AlbrechtL/10BASE-T1L/png/before pd xfmr w pd in reset 31V.png

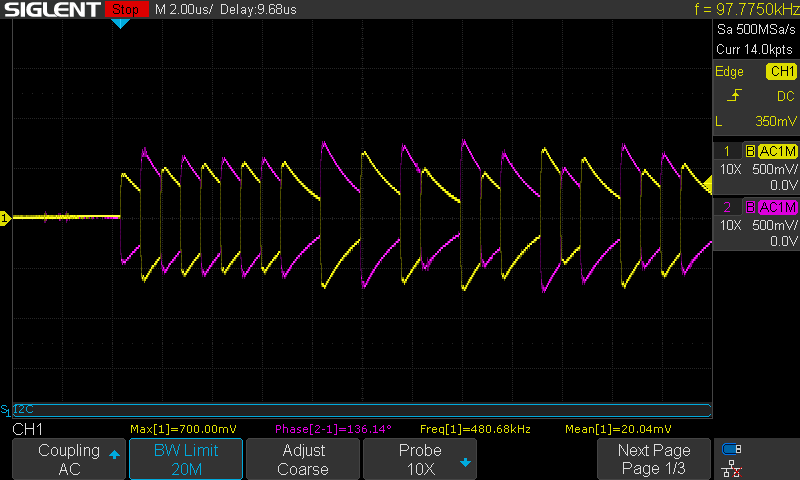
png/before pd xfmr w pd in reset 31V.png
