AlbrechtL/10BASE-T1L/png/SDS00017.png

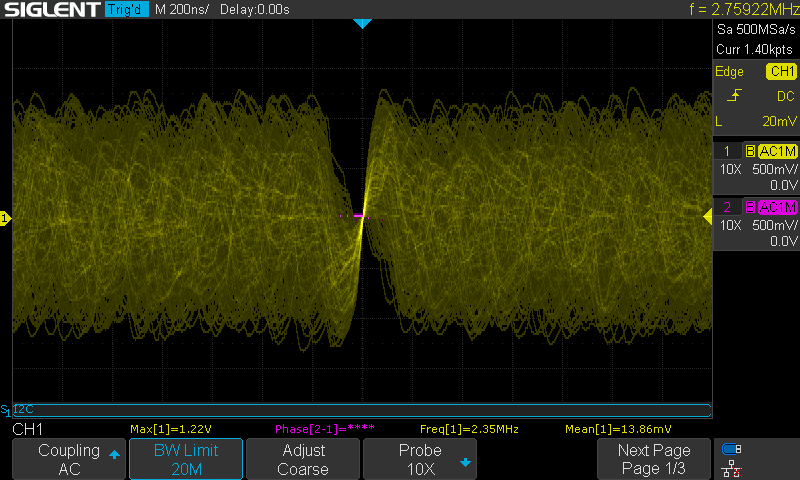
png/SDS00017.png
