AlbrechtL/10BASE-T1L/png/SDS00018.png

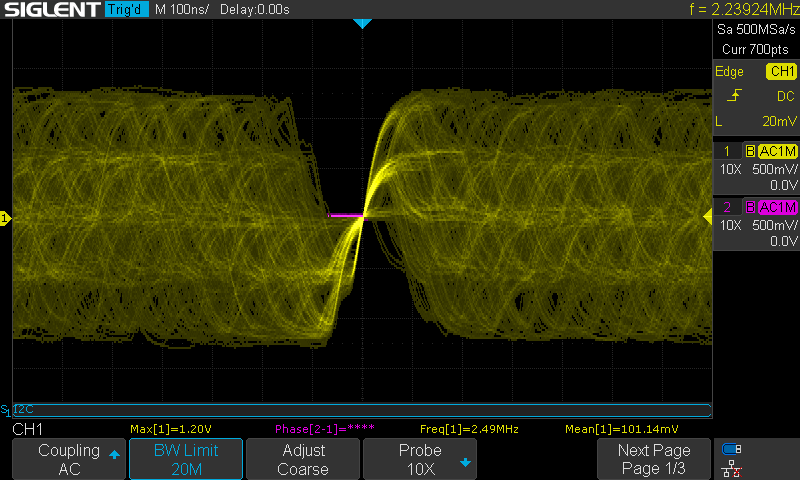
png/SDS00018.png
