AlbrechtL/10BASE-T1L/png/SDS00020.png

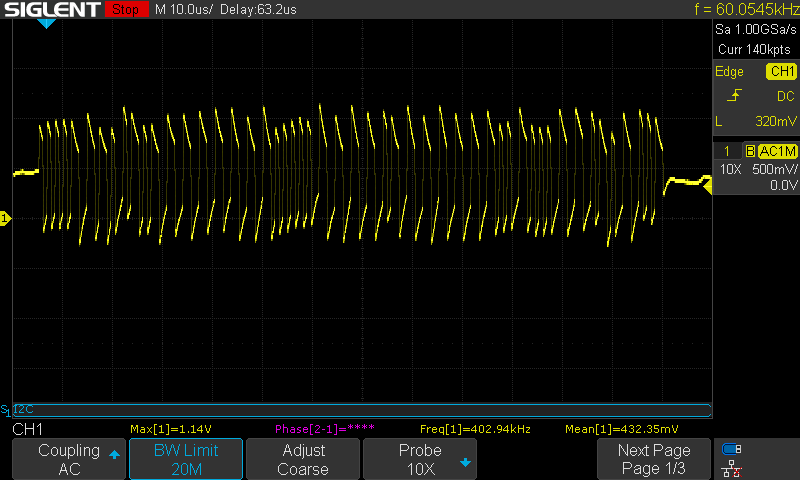
png/SDS00020.png
