AlbrechtL/10BASE-T1L/png/SDS00022.png

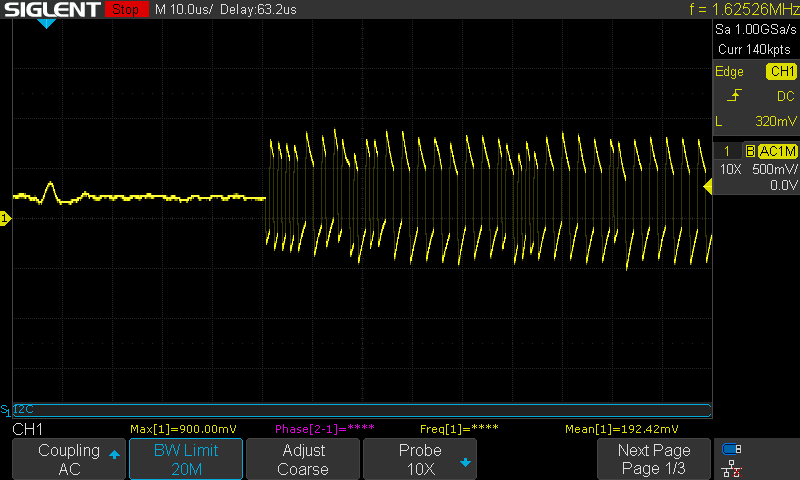
png/SDS00022.png
