AlbrechtL/10BASE-T1L/png/SDS00023.png

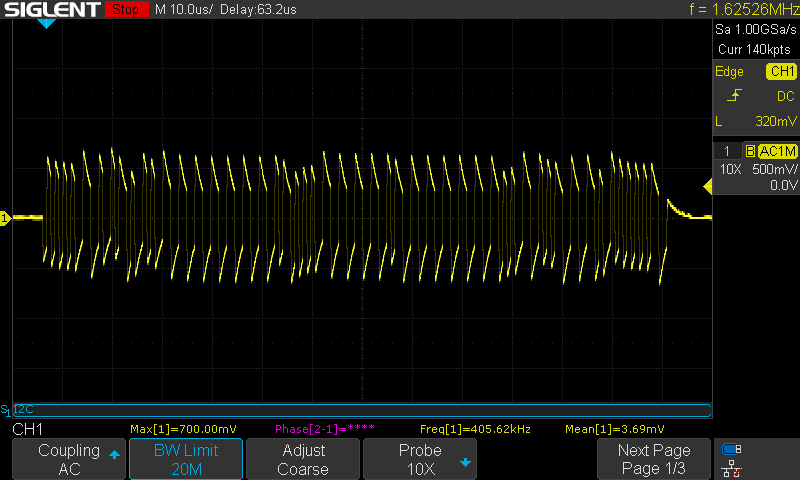
png/SDS00023.png
