AlbrechtL/10BASE-T1L/png/SDS00024.png

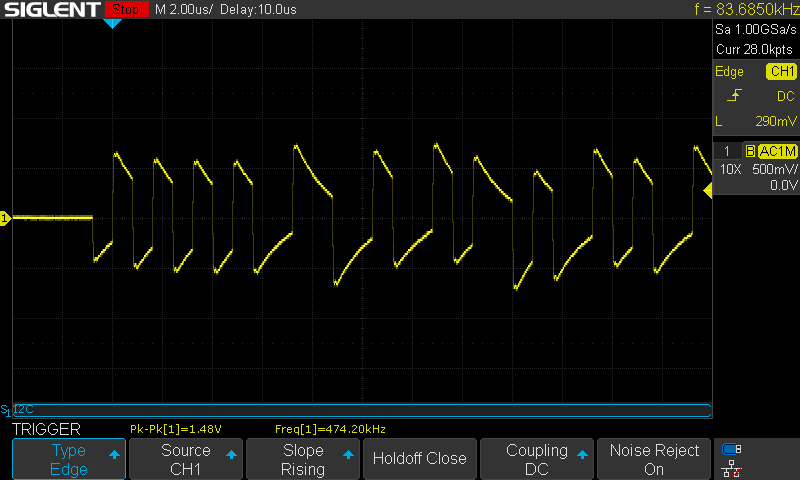
png/SDS00024.png
