AlbrechtL/10BASE-T1L/png/SDS00025.png

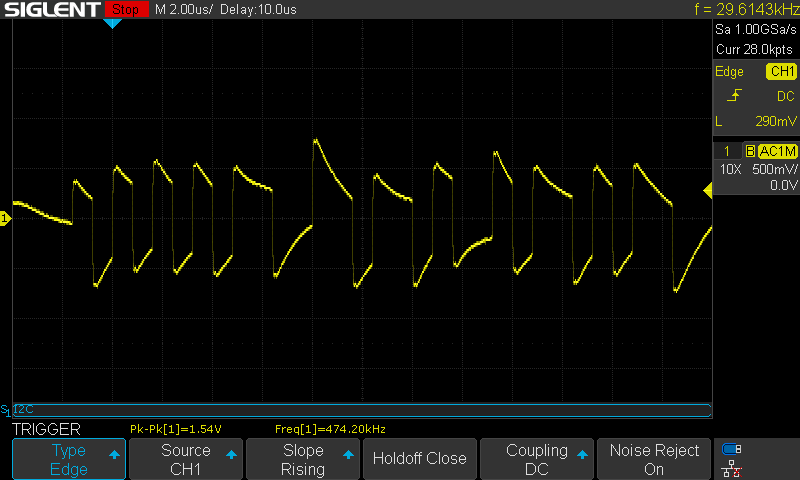
png/SDS00025.png
