AlbrechtL/10BASE-T1L/png/SDS00026.png

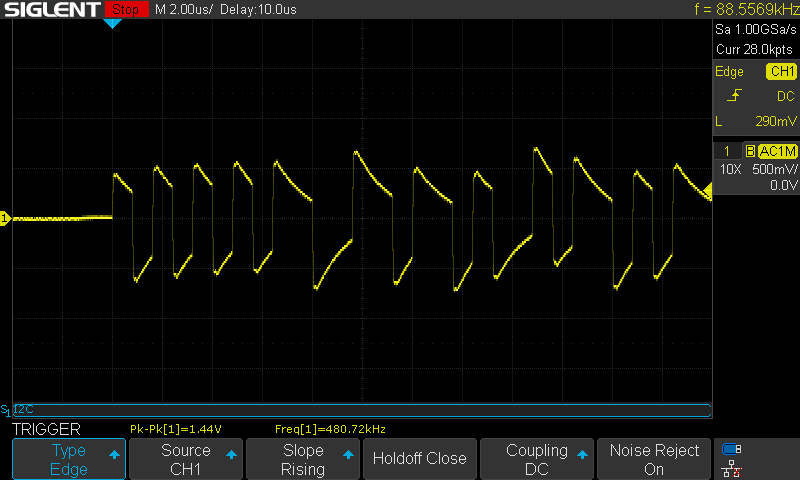
png/SDS00026.png
