AlbrechtL/10BASE-T1L/png/SDS00030.png

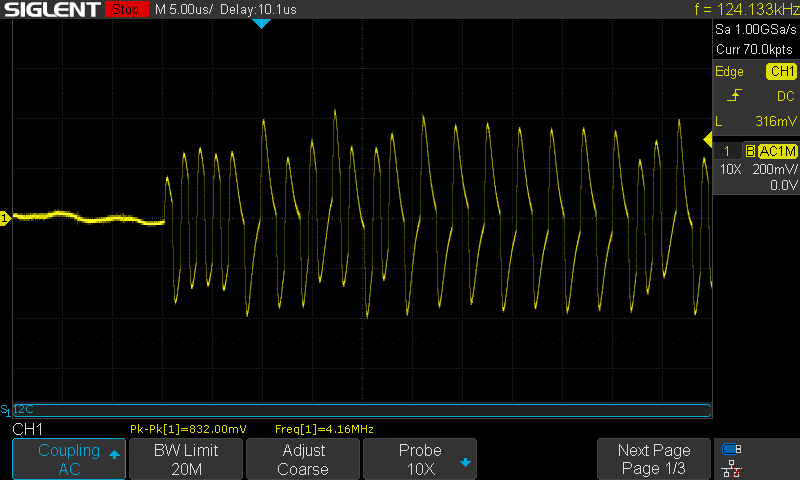
png/SDS00030.png
