AlbrechtL/10BASE-T1L/png/SDS00031.png

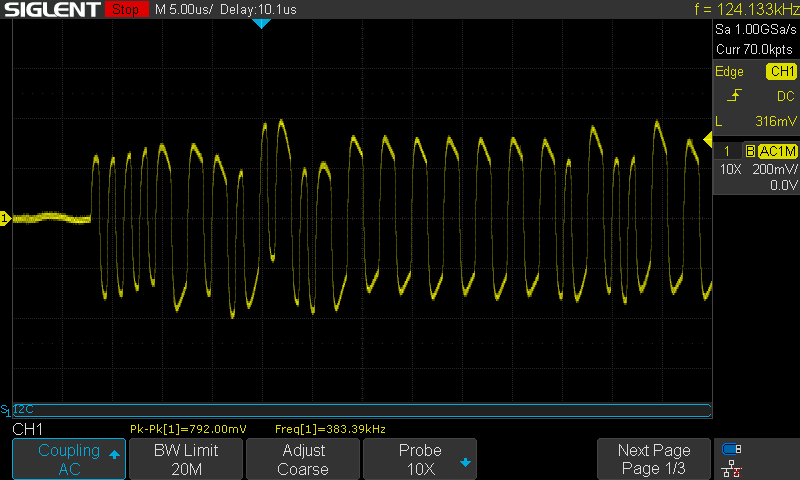
png/SDS00031.png
