AlbrechtL/10BASE-T1L/png/SDS00033.png

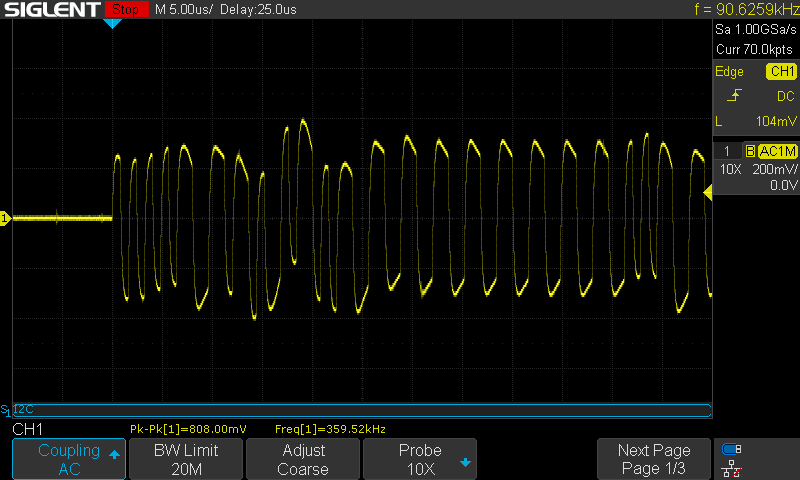
png/SDS00033.png
