AlbrechtL/10BASE-T1L/png/SDS00034.png

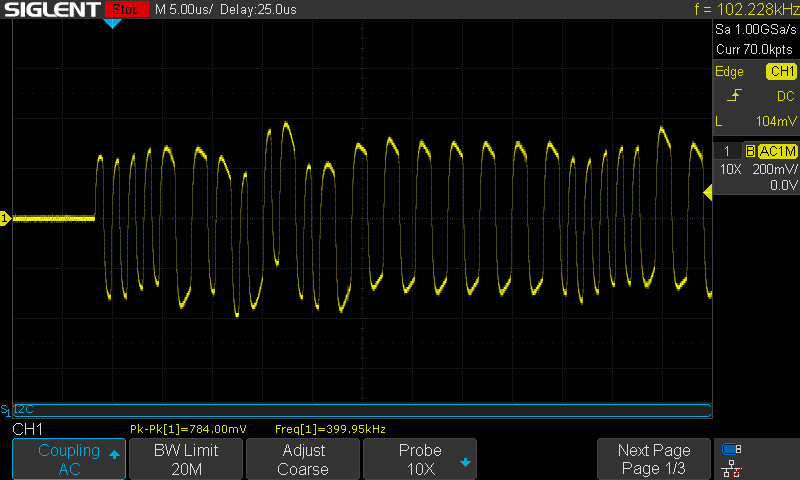
png/SDS00034.png
