AlbrechtL/10BASE-T1L/png/SDS00035.png

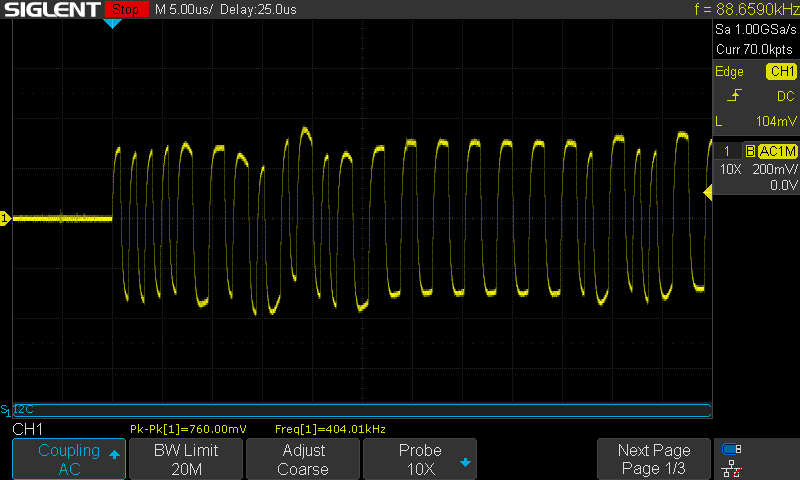
png/SDS00035.png
