AlbrechtL/10BASE-T1L/png/SDS00036.png

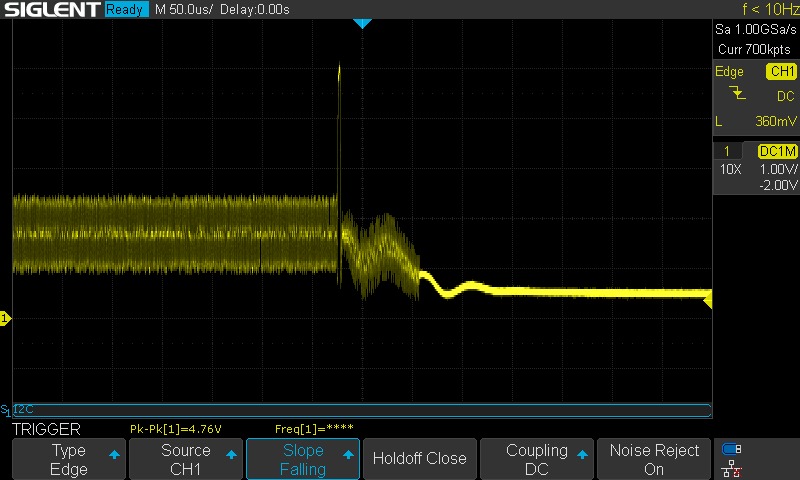
png/SDS00036.png
