AlbrechtL/10BASE-T1L/png/SDS00037.png

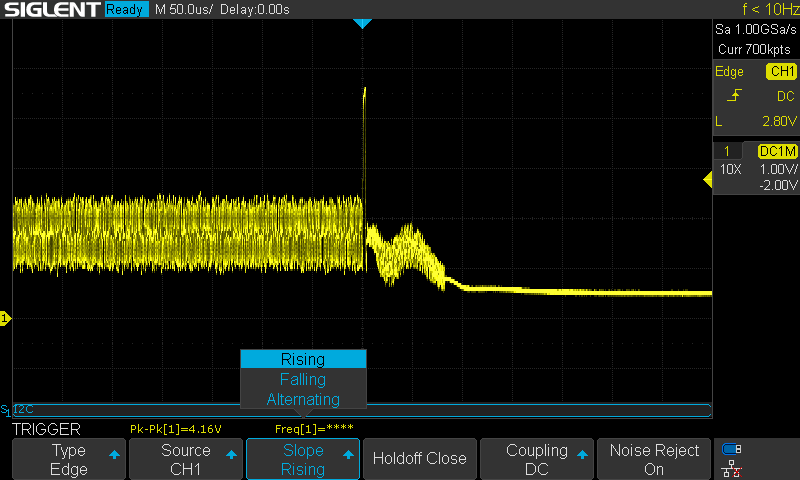
png/SDS00037.png
