AlbrechtL/10BASE-T1L/png/SDS00038.png

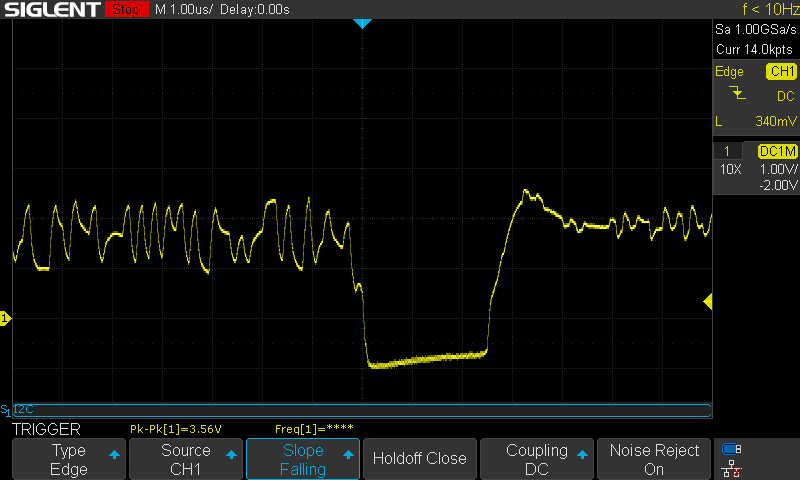
png/SDS00038.png
