AlbrechtL/10BASE-T1L/png/SDS00039.png

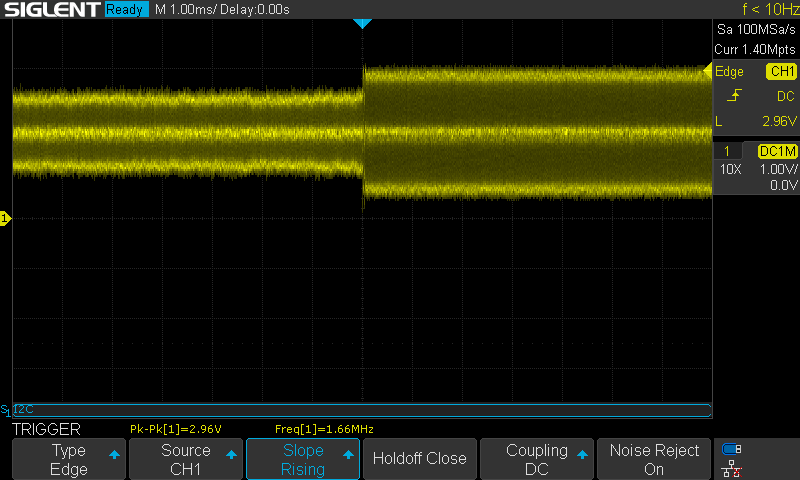
png/SDS00039.png
