AlbrechtL/10BASE-T1L/png/SDS00040.png

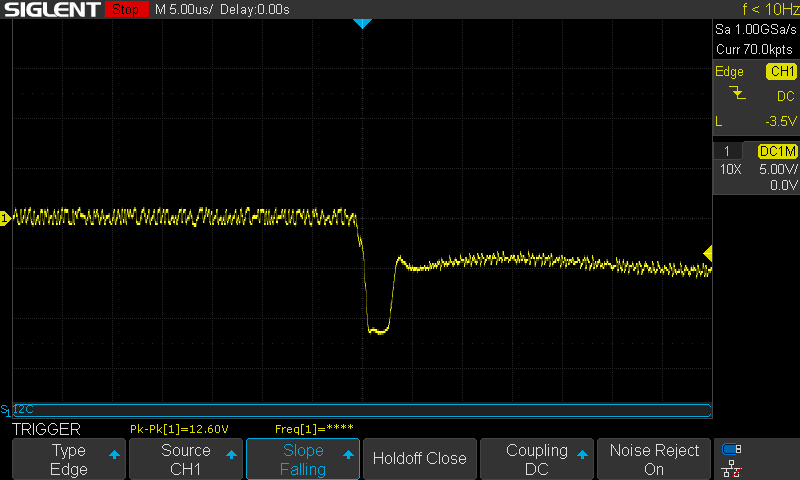
png/SDS00040.png
