AlbrechtL/10BASE-T1L/png/SDS00044.png

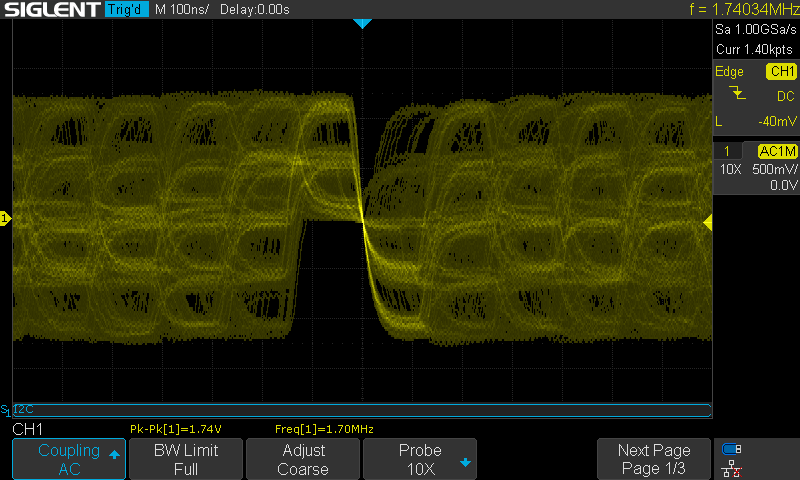
png/SDS00044.png
