AlbrechtL/10BASE-T1L/png/SDS00046.png

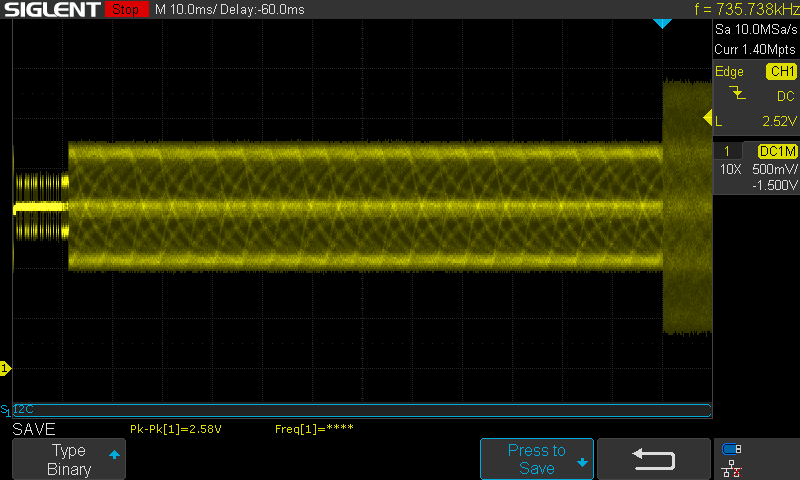
png/SDS00046.png
