AlbrechtL/10BASE-T1L/png/SDS00047.png

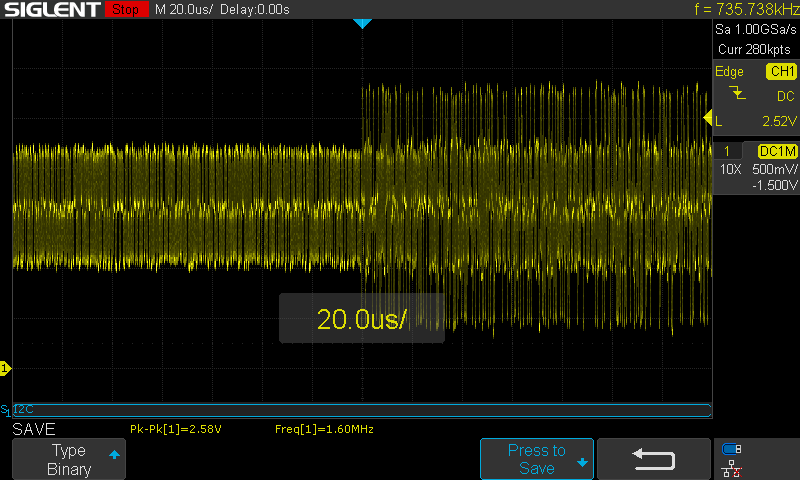
png/SDS00047.png
