AlbrechtL/10BASE-T1L/png/SDS00048.png

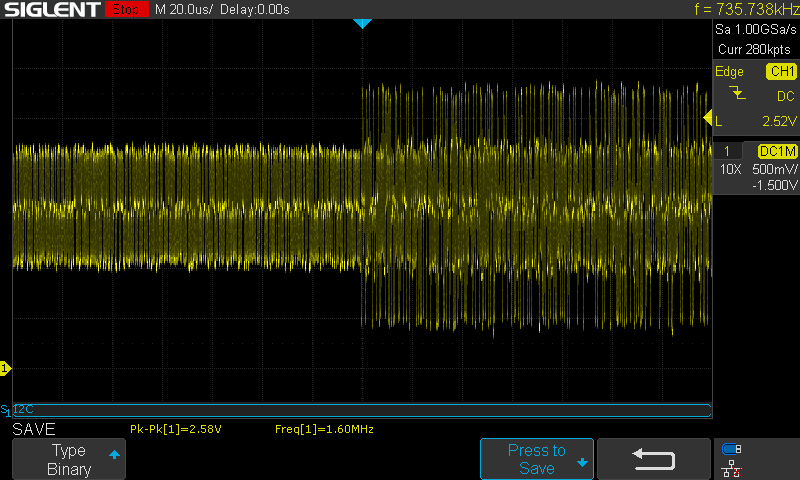
png/SDS00048.png
