AlbrechtL/10BASE-T1L/png/SDS00049.png

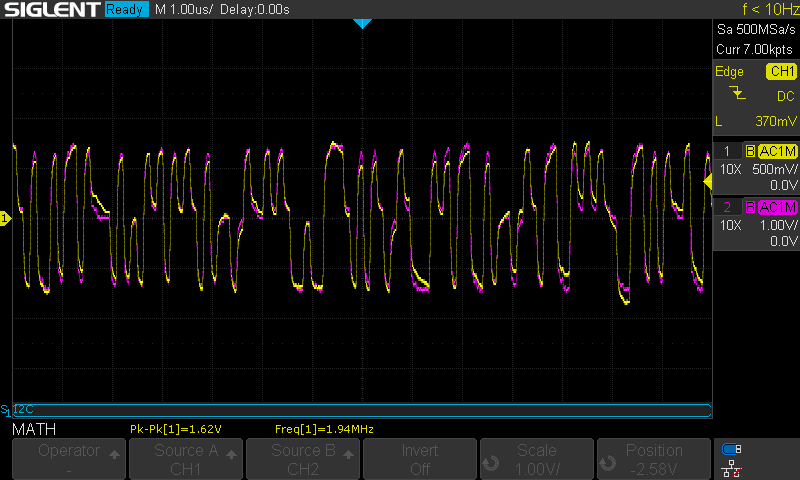
png/SDS00049.png
