AlbrechtL/10BASE-T1L/png/SDS00050.png

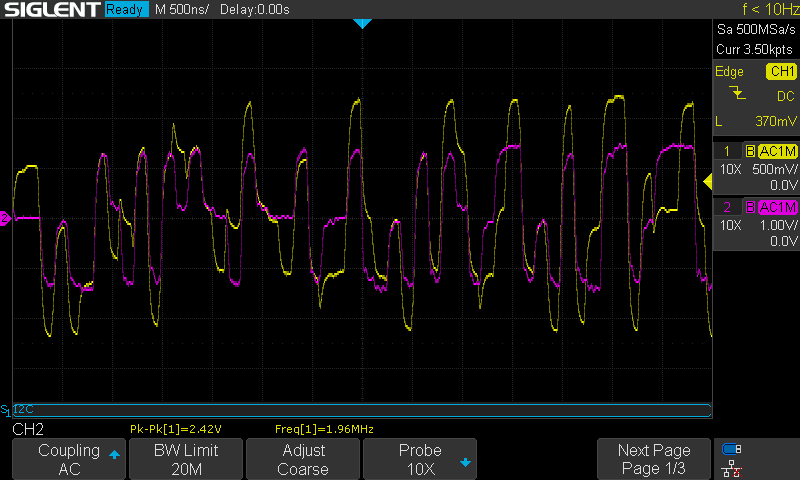
png/SDS00050.png
