AlbrechtL/10BASE-T1L/png/SDS00051.png

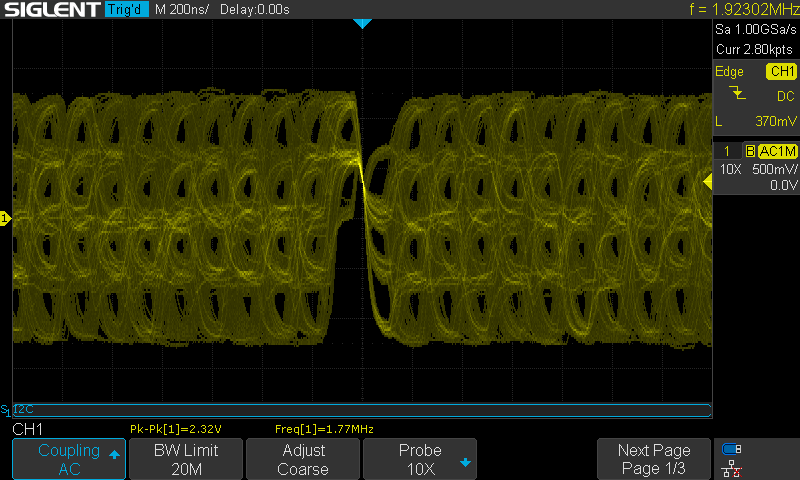
png/SDS00051.png
