AlbrechtL/10BASE-T1L/png/SDS00052.png

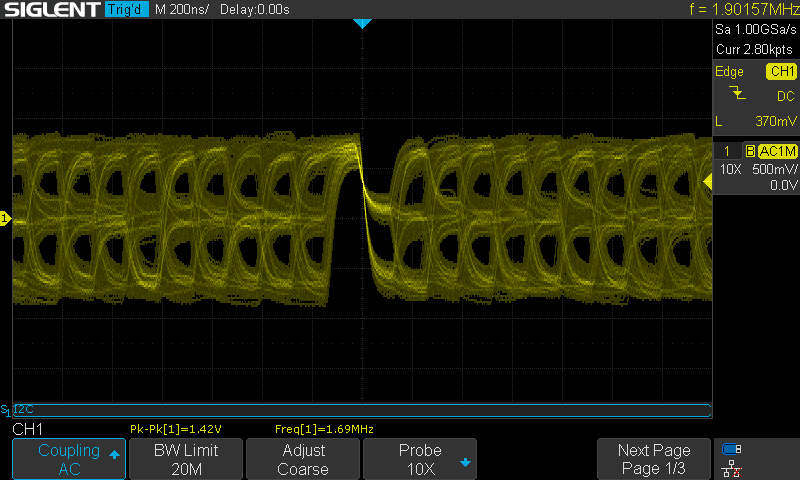
png/SDS00052.png
