AlbrechtL/10BASE-T1L/png/SDS00059.png

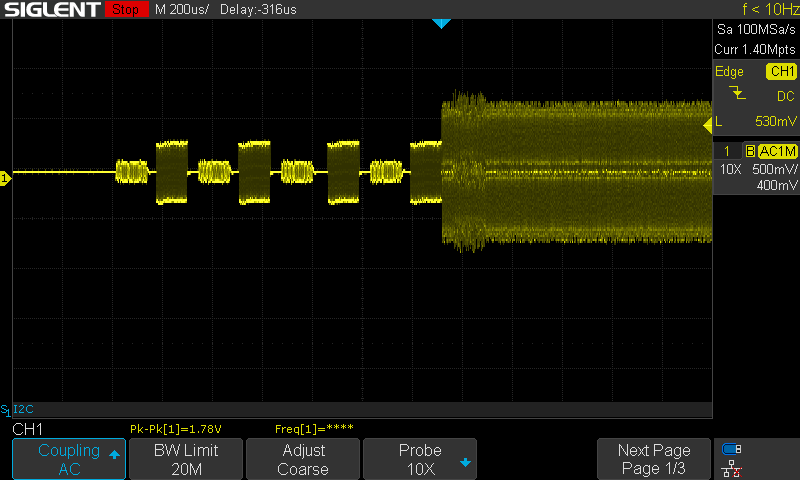
png/SDS00059.png
