AlbrechtL/10BASE-T1L/png/SDS00060.png

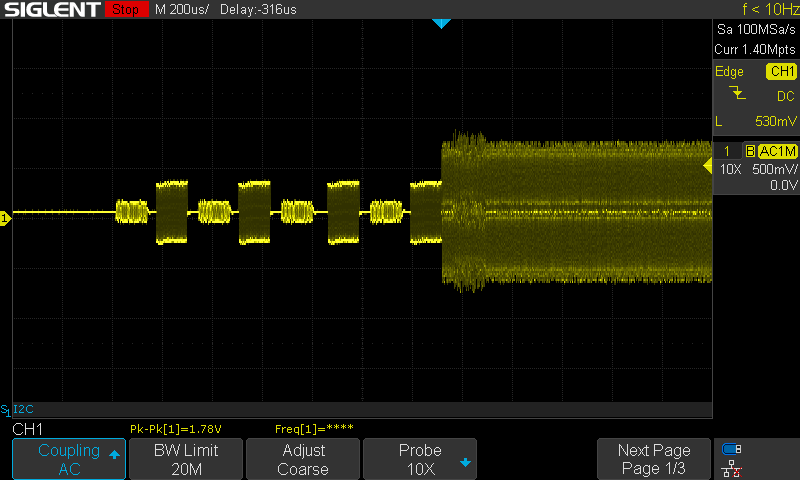
png/SDS00060.png
