AlbrechtL/10BASE-T1L/png/SDS00061.png

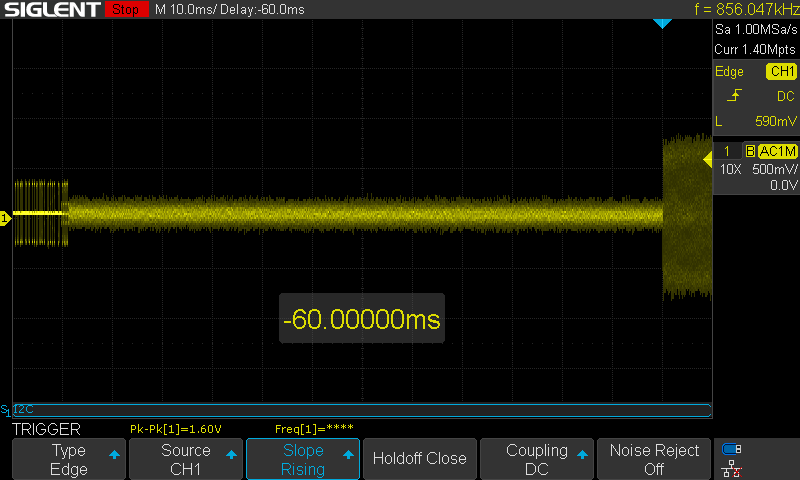
png/SDS00061.png
