AlbrechtL/10BASE-T1L/png/SDS00062.png

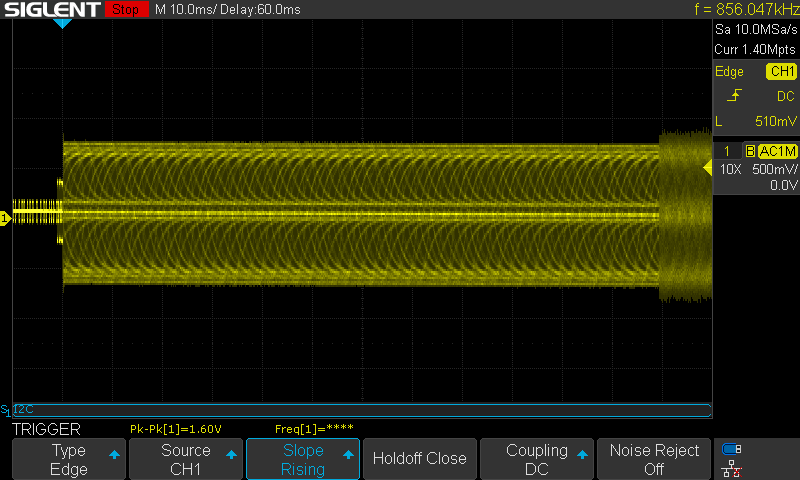
png/SDS00062.png
