AlbrechtL/10BASE-T1L/png/SDS00064.png

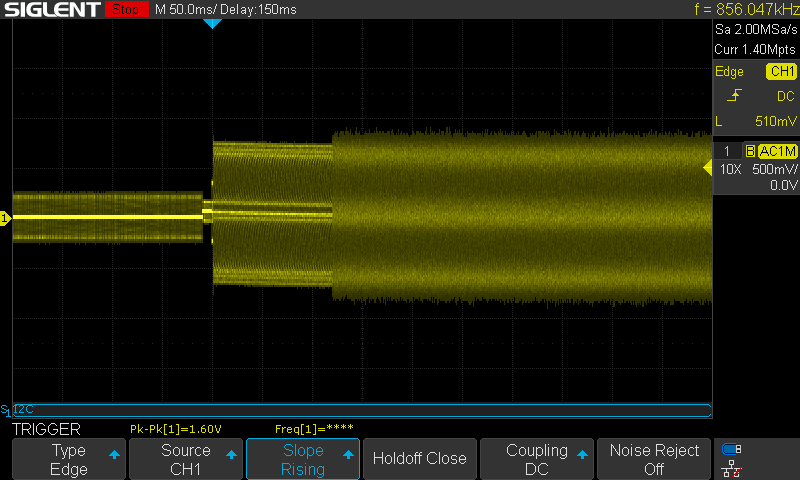
png/SDS00064.png
