AlbrechtL/10BASE-T1L/png/SDS00065.png

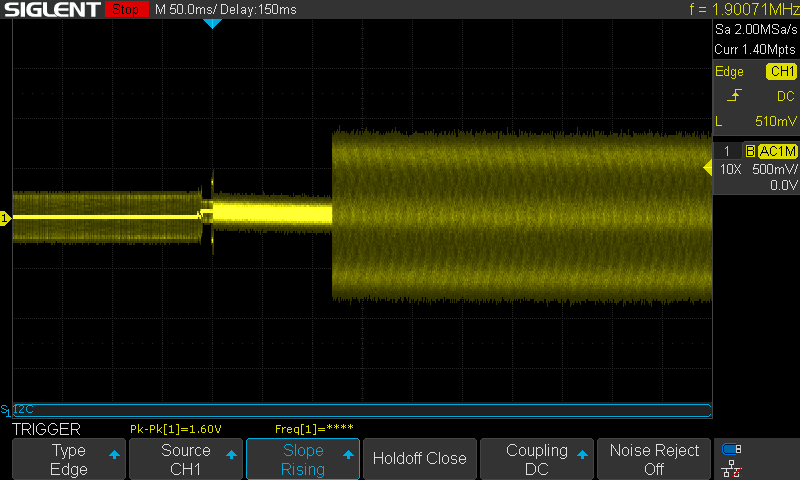
png/SDS00065.png
