AlbrechtL/10BASE-T1L/png/SDS00066.png

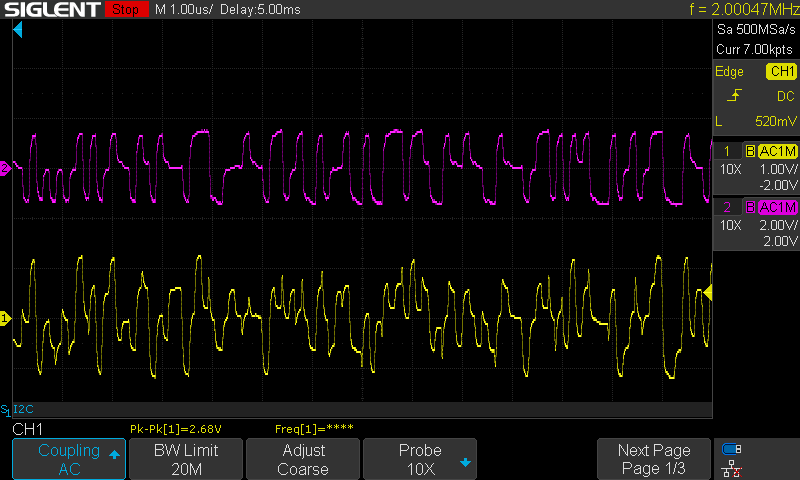
png/SDS00066.png
