AlbrechtL/10BASE-T1L/png/SDS00067.png

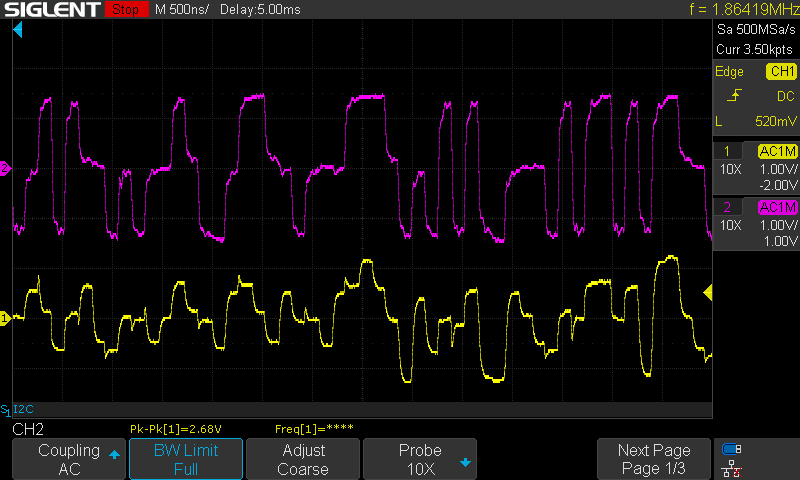
png/SDS00067.png
