AlbrechtL/10BASE-T1L/png/SDS00068.png

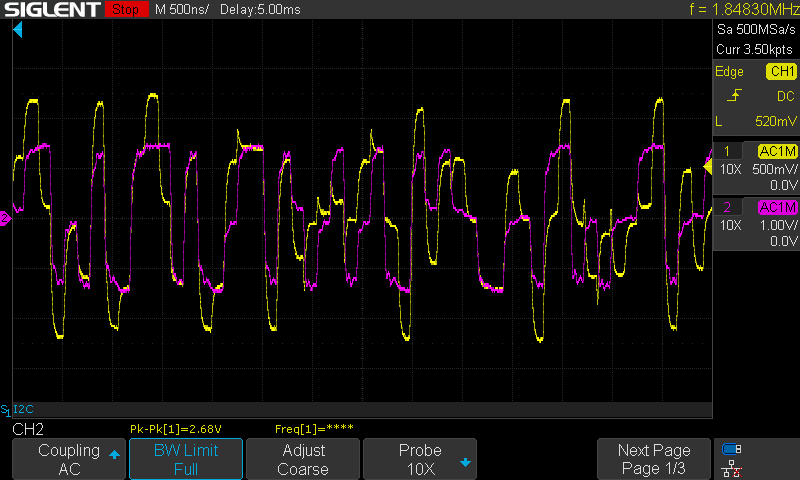
png/SDS00068.png
