AlbrechtL/10BASE-T1L/ref/50R.png

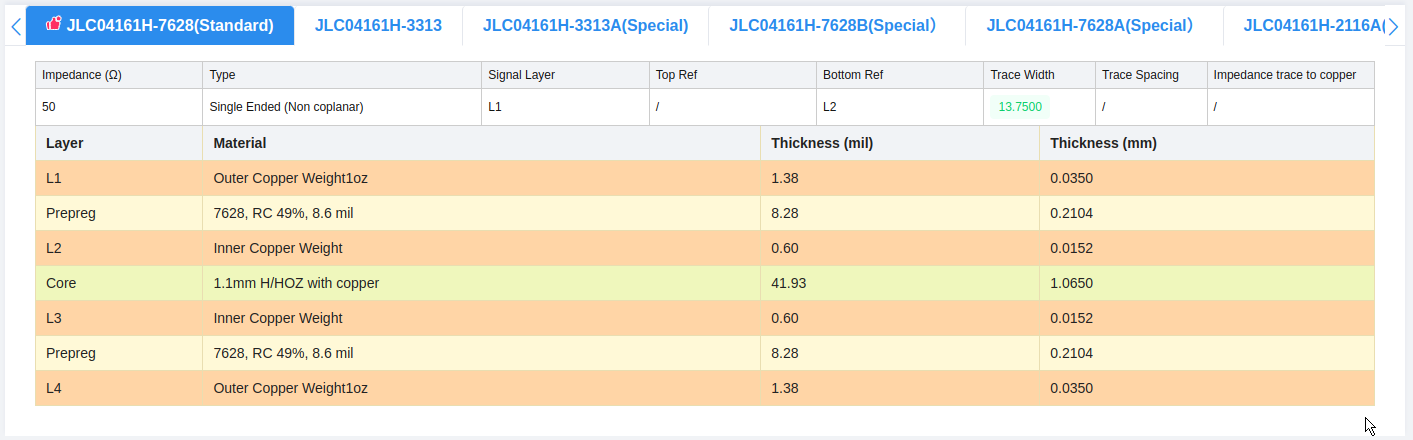
ref/50R.png
