AlbrechtL/10BASE-T1L/sim/hybrid.asc

B1: bv; V=(sgn(rand(1e3*time)-0.5)+1)/2
B2: bv; V=(sgn(rand(1e3*time+10000)-0.5)+1)/2
R1: res; 50
R2: res; 50
R3: res; 20k
R4: res; 10k
R5: res; 20k
R6: res; 20k
R7: res; 20k
R8: res; 20k
R9: res; 10k
R10: res; 20k
R11: res; 20k
R12: res; 20k
U1: UniversalOpAmp2
U2: UniversalOpAmp2
V1: voltage; 1
Named nets: 0, TX1, TX2, vcc, vc, RX1, RX2
.tran 0 0.1 0 10u
