AlbrechtL/10BASE-T1L/sim/MDI Return Loss.asc

C1: cap; 5pF
C2: cap; 0.47µF
C3: cap; 0.47µF
C4: cap; 1nF
C5: cap; 1nF
C6: cap; {c_clamp}
C7: cap; {c_clamp}
C8: cap; 10µ
L1: ind2; {cmc}
L2: ind2; {cmc}
L3: ind2; {dmc}
L4: ind2; {dmc}
L5: ind2; {cmc_lkg}; Rser=0.3
L6: ind2; {cmc_lkg}; Rser=0.3
L7: ind2; {dmc_lkg}; Rser=0.3
L8: ind2; {dmc_lkg}; Rser=0.3
L9: ind2; {xfmr}
L10: ind2; {xfmr}
R1: res; 100
R2: res; 1k
R3: res; 1k
V1: voltage; ""; AC 1 0
Named nets: 0
.param c_clamp=0.65pF xfmr=200uH cmc=1mH cmc_lkg=80nH dmc=1mH dmc_lkg=80nH
;tran 1
.ac dec 100 10k 20e6
k1 l1 l2 1
k2 l3 l4 1
k3 l9 l10 1
(100+1/I(V1))/(100-1/I(V1))
